drinow/MyNixieClock/MyNixie/Version2.0/Software/User/other.c

#include "other.h"

//显示数据，用1Byte表示1bit
uint8_t Nixie_HC595_Data[4][10]={0};

void Nixie_Delay(void)
{
  u32 i=0,j=0;
  for(;j<3;j++)
    for(;i<0xfffff;i++);
}

//把要点亮的数字坐标传给对应的位。
//参数：数字的行列坐标，和是否应该点亮
void Nixie_HC595_Num2Bit(u8 row,u8 line,u8 value)
{
  u8 product=0;
  product=(row+1)*10+line;
  switch((row+1)*10)//先大致分为4类，可减少判断次数
  {
    case 10:
    {
      switch(product)
      {
        case 10:if(value) HC595_Data[4]|= (1ul<<7); else HC595_Data[4]&=~(1ul<<7);break;
        case 11:if(value) HC595_Data[4]|= (1ul<<6); else HC595_Data[4]&=~(1ul<<6);break;
        case 12:if(value) HC595_Data[4]|= (1ul<<5); else HC595_Data[4]&=~(1ul<<5);break;
        case 13:if(value) HC595_Data[4]|= (1ul<<4); else HC595_Data[4]&=~(1ul<<4);break;
        case 14:if(value) HC595_Data[4]|= (1ul<<3); else HC595_Data[4]&=~(1ul<<3);break;
        case 15:if(value) HC595_Data[4]|= (1ul<<2); else HC595_Data[4]&=~(1ul<<2);break;
        case 16:if(value) HC595_Data[4]|= (1ul<<1); else HC595_Data[4]&=~(1ul<<1);break;
        case 17:if(value) HC595_Data[4]|= (1ul<<0); else HC595_Data[4]&=~(1ul<<0);break;
        case 18:if(value) HC595_Data[3]|= (1ul<<7); else HC595_Data[3]&=~(1ul<<7);break;
        case 19:if(value) HC595_Data[3]|= (1ul<<6); else HC595_Data[3]&=~(1ul<<6);break;
      }
    }
    break;
    case 20:
    {
      switch(product)
      {
        case 20:if(value) HC595_Data[3]|= (1ul<<5); else HC595_Data[3]&=~(1ul<<5);break;
        case 21:if(value) HC595_Data[3]|= (1ul<<4); else HC595_Data[3]&=~(1ul<<4);break;
        case 22:if(value) HC595_Data[3]|= (1ul<<3); else HC595_Data[3]&=~(1ul<<3);break;
        case 23:if(value) HC595_Data[3]|= (1ul<<2); else HC595_Data[3]&=~(1ul<<2);break;
        case 24:if(value) HC595_Data[3]|= (1ul<<1); else HC595_Data[3]&=~(1ul<<1);break;
        case 25:if(value) HC595_Data[3]|= (1ul<<0); else HC595_Data[3]&=~(1ul<<0);break;
        case 26:if(value) HC595_Data[2]|= (1ul<<7); else HC595_Data[2]&=~(1ul<<7);break;
        case 27:if(value) HC595_Data[2]|= (1ul<<6); else HC595_Data[2]&=~(1ul<<6);break;
        case 28:if(value) HC595_Data[2]|= (1ul<<5); else HC595_Data[2]&=~(1ul<<5);break;
        case 29:if(value) HC595_Data[2]|= (1ul<<4); else HC595_Data[2]&=~(1ul<<4);break;
      }
    }
    break;
    case 30:
    {
      switch(product)
      {
        case 30:if(value) HC595_Data[2]|= (1ul<<3); else HC595_Data[2]&=~(1ul<<3);break;
        case 31:if(value) HC595_Data[2]|= (1ul<<2); else HC595_Data[2]&=~(1ul<<2);break;
        case 32:if(value) HC595_Data[2]|= (1ul<<1); else HC595_Data[2]&=~(1ul<<1);break;
        case 33:if(value) HC595_Data[2]|= (1ul<<0); else HC595_Data[2]&=~(1ul<<0);break;
        case 34:if(value) HC595_Data[1]|= (1ul<<7); else HC595_Data[1]&=~(1ul<<7);break;
        case 35:if(value) HC595_Data[1]|= (1ul<<6); else HC595_Data[1]&=~(1ul<<6);break;
        case 36:if(value) HC595_Data[1]|= (1ul<<5); else HC595_Data[1]&=~(1ul<<5);break;
        case 37:if(value) HC595_Data[1]|= (1ul<<4); else HC595_Data[1]&=~(1ul<<4);break;
        case 38:if(value) HC595_Data[1]|= (1ul<<3); else HC595_Data[1]&=~(1ul<<3);break;
        case 39:if(value) HC595_Data[1]|= (1ul<<2); else HC595_Data[1]&=~(1ul<<2);break;
      }
    }
    break;
    case 40:
    {
      switch(product)
      {
        case 40:if(value) HC595_Data[1]|= (1ul<<1); else HC595_Data[1]&=~(1ul<<1);break;
        case 41:if(value) HC595_Data[1]|= (1ul<<0); else HC595_Data[1]&=~(1ul<<0);break;
        case 42:if(value) HC595_Data[0]|= (1ul<<7); else HC595_Data[0]&=~(1ul<<7);break;
        case 43:if(value) HC595_Data[0]|= (1ul<<6); else HC595_Data[0]&=~(1ul<<6);break;
        case 44:if(value) HC595_Data[0]|= (1ul<<5); else HC595_Data[0]&=~(1ul<<5);break;
        case 45:if(value) HC595_Data[0]|= (1ul<<4); else HC595_Data[0]&=~(1ul<<4);break;
        case 46:if(value) HC595_Data[0]|= (1ul<<3); else HC595_Data[0]&=~(1ul<<3);break;
        case 47:if(value) HC595_Data[0]|= (1ul<<2); else HC595_Data[0]&=~(1ul<<2);break;
        case 48:if(value) HC595_Data[0]|= (1ul<<1); else HC595_Data[0]&=~(1ul<<1);break;
        case 49:if(value) HC595_Data[0]|= (1ul<<0); else HC595_Data[0]&=~(1ul<<0);break;
      }
    }
    break;
    default:break;
  }
}

//将显示数据装载到595的输入缓存数组中
void Nixie_Load(u8 array[][10])
{
  u8 row,line;
  for(row=0;row<4;row++)
    for(line=0;line<10;line++)
  {
    Nixie_HC595_Num2Bit(row,line,array[row][line]);
  }
}

//将595的输入缓存数组的数据输出到595上
void Nixie_Update(void)
{
  hc595_WriteBytes(HC595_Data,sizeof(HC595_Data));
}

//自检程序。
void Nixie_Test(void)
{
    u8 state=0;
    u8 row;

    __disable_irq();
    memset((u8*)WS2812_RGB,0,sizeof(WS2812_RGB));
    WS2812_Send_Px();
    __enable_irq();

    Nixie_Light_Ctl(100);
    for(;state<10;state++)
    {
        //循环点亮
        memset(Nixie_HC595_Data,0,sizeof(Nixie_HC595_Data));
        for(row=0;row<4;row++)
        {
          Nixie_HC595_Data[row][state]=1;
        }

        Nixie_Load(Nixie_HC595_Data);
        Nixie_Update();

        Nixie_Delay();
    }
}


//将时间数据转换到HC595数组中。
extern __IO u16 LightLevel;
extern __IO u8 ForceLightOn;
void Nixie_TimeToHC595(void)
{
  memset(Nixie_HC595_Data,0,sizeof(Nixie_HC595_Data));
  Nixie_HC595_Data[0][GetTime.hour>>4]=1;
  Nixie_HC595_Data[1][GetTime.hour&0x0F]=1;
  Nixie_HC595_Data[2][GetTime.min>>4]=1;
  Nixie_HC595_Data[3][GetTime.min&0x0F]=1;
  
  Nixie_Load(Nixie_HC595_Data);
  Nixie_Update();
  
  if(LightLevel||ForceLightOn)
    Dot_Toggle();
  else
  {
    Dot1_OFF;Dot2_OFF;
  }
}

//将日期数据转换到HC595数组中。
void Nixie_DateToHC595(void)
{
  memset(Nixie_HC595_Data,0,sizeof(Nixie_HC595_Data));
  Nixie_HC595_Data[0][GetTime.month>>4]=1;
  Nixie_HC595_Data[1][GetTime.month&0x0F]=1;
  Nixie_HC595_Data[2][GetTime.date>>4]=1;
  Nixie_HC595_Data[3][GetTime.date&0x0F]=1;
  
	Dot1_OFF;Dot2_ON;
  Nixie_Load(Nixie_HC595_Data);
  Nixie_Update();
}

//将星期数据转换到HC595数组中。
void Nixie_WeekToHC595(void)
{
  memset(Nixie_HC595_Data,0,sizeof(Nixie_HC595_Data));

  Nixie_HC595_Data[2][GetTime.week>>4]=1;
  Nixie_HC595_Data[3][GetTime.week&0x0F]=1;
  
	Dot1_ON;Dot2_OFF;
  Nixie_Load(Nixie_HC595_Data);
  Nixie_Update();
}

//将温度数据转换到HC595数组中。
void Nixie_TempToHC595(void)
{
    memset(Nixie_HC595_Data,0,sizeof(Nixie_HC595_Data));

    Nixie_HC595_Data[0][(u8)(SHT20.HUMI_POLL)/10]=1;
    Nixie_HC595_Data[1][(u8)(SHT20.HUMI_POLL)%10]=1;
    Nixie_HC595_Data[2][(u8)((DS18B20_Temp+SHT20.TEMP_POLL)/2)/10]=1;
    Nixie_HC595_Data[3][(u8)((DS18B20_Temp+SHT20.TEMP_POLL)/2)%10]=1;

    Dot1_ON;Dot2_ON;
    Nixie_Load(Nixie_HC595_Data);
    Nixie_Update();
}


extern u8 SetChannel;
extern u8 NewNum;
u8 ChannelFlash=0;
extern u8  __IO Period_1S;
void Set_TimeToHC595(void)
{
	static u8 toggle=0;
  //按键按下
  if(NewNum!=0xff)
  {
    switch(SetChannel)
    {
      case CHANNEL0:if(NewNum>2)NewNum=0; SetTime.hour=(SetTime.hour&0x0f)|(NewNum<<4);NewNum=0xff; break;
      case CHANNEL1:if(SetTime.hour>=0x20&&NewNum>4)NewNum=4;SetTime.hour=(SetTime.hour&0xf0)|NewNum;NewNum=0xff;break;
      case CHANNEL2:if(NewNum>6)NewNum=0;SetTime.min=(SetTime.min&0x0f)|(NewNum<<4);NewNum=0xff;break;
      case CHANNEL3:SetTime.min=(SetTime.min&0xf0)|NewNum;NewNum=0xff;break;
      default :break;
    }
    SetChannel++;if(SetChannel>=4)SetChannel=0;
  }
  
  memset(Nixie_HC595_Data,0,sizeof(Nixie_HC595_Data));
  Nixie_HC595_Data[0][SetTime.hour>>4]=1;
  Nixie_HC595_Data[1][SetTime.hour&0x0F]=1;
  Nixie_HC595_Data[2][SetTime.min>>4]=1;
  Nixie_HC595_Data[3][SetTime.min&0x0F]=1;

  //被选中的通道闪烁
  if(ChannelFlash)
  {
    switch(SetChannel)
    {
      case CHANNEL0:Nixie_HC595_Data[0][SetTime.hour>>4]=0;break;
      case CHANNEL1:Nixie_HC595_Data[1][SetTime.hour&0x0F]=0;break;
      case CHANNEL2:Nixie_HC595_Data[2][SetTime.min>>4]=0;break;
      case CHANNEL3:Nixie_HC595_Data[3][SetTime.min&0x0F]=0;break;
      default :break;
    }
  }
    
  Nixie_Load(Nixie_HC595_Data);
  Nixie_Update();
  
	if(toggle)
	{
		toggle=~toggle;
		Dot1_ON;Dot2_ON;
	}
	else
	{
		toggle=~toggle;
		Dot1_OFF;Dot2_OFF;
	}
}

void Set_DateToHC595(void)
{
  if(NewNum!=0xff)
  {
    switch(SetChannel)
    {
      case CHANNEL0:if(NewNum>2)NewNum=0;SetTime.month=(SetTime.month&0x0f)|(NewNum<<4);NewNum=0xff;break;
      case CHANNEL1:SetTime.month=(SetTime.month&0xf0)|NewNum;NewNum=0xff;break;
      case CHANNEL2:if(NewNum>3)NewNum=0;SetTime.date=(SetTime.date&0x0f)|(NewNum<<4);NewNum=0xff;break;
      case CHANNEL3:if(SetTime.date>=0x30&&NewNum>1)NewNum=0;SetTime.date=(SetTime.date&0xf0)|NewNum;NewNum=0xff;break;
      default :break;
    }
    SetChannel++;if(SetChannel>=4)SetChannel=0;
  }
  
  memset(Nixie_HC595_Data,0,sizeof(Nixie_HC595_Data));
  Nixie_HC595_Data[0][SetTime.month>>4]=1;
  Nixie_HC595_Data[1][SetTime.month&0x0F]=1;
  Nixie_HC595_Data[2][SetTime.date>>4]=1;
  Nixie_HC595_Data[3][SetTime.date&0x0F]=1;

  //被选中的通道闪烁
  if(ChannelFlash)
  {
    switch(SetChannel)
    {
      case CHANNEL0:Nixie_HC595_Data[0][SetTime.month>>4]=0;break;
      case CHANNEL1:Nixie_HC595_Data[1][SetTime.month&0x0F]=0;break;
      case CHANNEL2:Nixie_HC595_Data[2][SetTime.date>>4]=0;break;
      case CHANNEL3:Nixie_HC595_Data[3][SetTime.date&0x0F]=0;break;
      default :break;
    }
  }
    
  Nixie_Load(Nixie_HC595_Data);
  Nixie_Update();
  
  Dot1_ON;Dot2_ON;
}

void Set_WeekToHC595(void)
{
  if(SetChannel<3)SetChannel=3;
  
  if(NewNum!=0xff)
  {
    switch(SetChannel)
    {
      case CHANNEL3:if(NewNum>7)NewNum=1;if(NewNum<1)NewNum=1;SetTime.week=(SetTime.week&0xf0)|NewNum;NewNum=0xff;break;
      default :break;
    }
    SetChannel++;if(SetChannel>=4)SetChannel=0;
  }
  
  memset(Nixie_HC595_Data,0,sizeof(Nixie_HC595_Data));
  Nixie_HC595_Data[3][SetTime.week&0x0F]=1;
  
  //被选中的通道闪烁
  if(ChannelFlash)
  {
    switch(SetChannel)
    {
      case CHANNEL3:Nixie_HC595_Data[3][SetTime.week&0x0F]=0;break;
      default :break;
    }
  }
    
  Nixie_Load(Nixie_HC595_Data);
  Nixie_Update();
  
  Dot1_OFF;Dot2_OFF;
}

void Set_YearToHC595(void)
{
  if(SetChannel<2)SetChannel=2;
  
  if(NewNum!=0xff)
  {
    switch(SetChannel)
    {
      case CHANNEL2:SetTime.year=(SetTime.year&0x0f)|(NewNum<<4);NewNum=0xff;break;
      case CHANNEL3:SetTime.year=(SetTime.year&0xf0)|NewNum;NewNum=0xff;break;
      default :break;
    }
    SetChannel++;if(SetChannel>=4)SetChannel=0;
  }
  
  memset(Nixie_HC595_Data,0,sizeof(Nixie_HC595_Data));
  Nixie_HC595_Data[0][2]=1;
  Nixie_HC595_Data[1][0]=1;
  Nixie_HC595_Data[2][SetTime.year>>4]=1;
  Nixie_HC595_Data[3][SetTime.year&0x0F]=1;

  //被选中的通道闪烁
  if(ChannelFlash)
  {
    switch(SetChannel)
    {
      case CHANNEL2:Nixie_HC595_Data[2][SetTime.year>>4]=0;break;
      case CHANNEL3:Nixie_HC595_Data[3][SetTime.year&0x0F]=0;break;
      default :break;
    }
  }
    
  Nixie_Load(Nixie_HC595_Data);
  Nixie_Update();
  
  Dot1_OFF;Dot2_OFF;
}

void Set_AlarmToHC595(void)
{
  //按键按下
  if(NewNum!=0xff)
  {
    switch(SetChannel)
    {
      case CHANNEL0:Alarm.hour=(Alarm.hour&0x0f)|(NewNum<<4);	NewNum=0xff; break;
      case CHANNEL1:Alarm.hour=(Alarm.hour&0xf0)|NewNum;			NewNum=0xff;break;
      case CHANNEL2:Alarm.min=(Alarm.min&0x0f)|(NewNum<<4);		NewNum=0xff;break;
      case CHANNEL3:Alarm.min=(Alarm.min&0xf0)|NewNum;				NewNum=0xff;break;
      default :break;
    }
    SetChannel++;if(SetChannel>=4)SetChannel=0;
  }
  
  memset(Nixie_HC595_Data,0,sizeof(Nixie_HC595_Data));
  Nixie_HC595_Data[0][Alarm.hour>>4]=1;
  Nixie_HC595_Data[1][Alarm.hour&0x0F]=1;
  Nixie_HC595_Data[2][Alarm.min>>4]=1;
  Nixie_HC595_Data[3][Alarm.min&0x0F]=1;

  //被选中的通道闪烁
  if(ChannelFlash)
  {
    switch(SetChannel)
    {
      case CHANNEL0:Nixie_HC595_Data[0][Alarm.hour>>4]=0;break;
      case CHANNEL1:Nixie_HC595_Data[1][Alarm.hour&0x0F]=0;break;
      case CHANNEL2:Nixie_HC595_Data[2][Alarm.min>>4]=0;break;
      case CHANNEL3:Nixie_HC595_Data[3][Alarm.min&0x0F]=0;break;
      default :break;
    }
    Dot1_ON;Dot2_OFF; 
  }
  else
  {
    Dot1_OFF;Dot2_ON; 
  }
    
  Nixie_Load(Nixie_HC595_Data);
  Nixie_Update();

}

extern u8 SetType;
void Nixie_Set_Show(void)
{
  switch(SetType)
  {
    case SETTIME:Set_TimeToHC595();break;
    case SETDATE:Set_DateToHC595();break;
    case SETWEEK:Set_WeekToHC595();break;
    case SETYEAR:Set_YearToHC595();break;
    case SETALARM:Set_AlarmToHC595();break;
    default:break;
  }
  ChannelFlash=~ChannelFlash;
}

//阴极保护程序，循环点亮其余未亮数字一小会
void Nixie_Cathode_Prevention(void)
{
  static u8 state=0;
  u32 i=0;
  uint8_t Nixie_Prevention_Data[4][10]={0};

  Nixie_Prevention_Data[0][state]=1;
  Nixie_Prevention_Data[1][state]=1;
  Nixie_Prevention_Data[2][state]=1;
  Nixie_Prevention_Data[3][state]=1;
  
  if((state++)==10)state=0;

  Nixie_Load(Nixie_Prevention_Data);
  Nixie_Update();
  
  for(i=0;i<0x5;i++);
  
  Nixie_Load(Nixie_HC595_Data);
  Nixie_Update();
}

void Nixie_Show(__IO u8 *state)
{
  static u8 cnt=0;
  switch(*state)
  {
    case DEFAULT:Nixie_TimeToHC595();break;
    case SHOWTEMP:Nixie_TempToHC595();cnt++;if(cnt>=4){cnt=0;Dot1_OFF;Dot2_OFF;*state=DEFAULT;Nixie_TimeToHC595();}break;
    case SHOWDATE:Nixie_DateToHC595();cnt++;if(cnt>=4){cnt=0;Dot1_OFF;Dot2_OFF;*state=DEFAULT;Nixie_TimeToHC595();}break;
    case SHOWWEEK:Nixie_WeekToHC595();cnt++;if(cnt>=4){cnt=0;Dot1_OFF;Dot2_OFF;*state=DEFAULT;Nixie_TimeToHC595();}break;
    default:break;
  }
}

extern __IO u16 LightLevel;
extern u8 Setting;
extern u8 SetChannel;
extern u8 SetType;
extern u8 NewNum;
extern u8 __IO ForceLightOn;
extern float Ruse,Guse,Buse;
float LightCoe=0;//亮度系数
void Nixie_DealRemote(__IO u8 *state)
{
  if(Setting==0)
  {
    switch(*state)
    {
        case DEFAULT:break;
        case SHOWSWITCH:  *state=DEFAULT;if(LightLevel==0)LightLevel=180;else {LightLevel=0;ForceLightOn=0;} 
                        Nixie_Light_Ctl(LightLevel);printf("LightLevel:%d\r\n",LightLevel);
                        EE_SaveConfig();
                        break;
        case LIGHT_UP:*state=DEFAULT;
                    LightLevel=LightLevel+20;if(LightLevel>=220)LightLevel=220;printf("LightLevel:%d\r\n",LightLevel);Nixie_Light_Ctl(LightLevel);
//                    LightCoe=LightCoe+0.15;if(LightCoe>=1)LightCoe=1;printf("LightCoe:%.1f\r\n",LightCoe);
                    EE_SaveConfig();
                    break;
        case LIGHT_DN:*state=DEFAULT;
                    LightLevel=LightLevel-20;if(LightLevel<=60)LightLevel=60;printf("LightLevel:%d\r\n",LightLevel);Nixie_Light_Ctl(LightLevel);
//                    LightCoe=LightCoe-0.15;if(LightCoe<=0.1)LightCoe=0.1;printf("LightCoe:%.1f\r\n",LightCoe);
                    EE_SaveConfig();
                    break;
        case PREV:  *state=DEFAULT;
                    LightCoe=LightCoe-0.15;if(LightCoe<=0.1)LightCoe=0.1;printf("LightCoe:%.1f\r\n",LightCoe);
                    EE_SaveConfig();
                    break;
        case NEXT:  *state=DEFAULT;
                    LightCoe=LightCoe+0.15;if(LightCoe>=1)LightCoe=1;printf("LightCoe:%.1f\r\n",LightCoe);
                    EE_SaveConfig();
                    break;
        case RGBSTATE:
                    *state=DEFAULT;
                    RGB_Msg.state++; 
                    if(RGB_Msg.state>=3)RGB_Msg.state=EFFECTS_ON;
//                    if(RGB_Msg.state==EFFECTS_OFF)
//                        {RGB_Msg.R=(u8)Ruse;RGB_Msg.G=(u8)Guse;RGB_Msg.B=(u8)Buse;}
                    if(RGB_Msg.state==EFFECTS_ON)//更新颜色信息
                        EE_SaveConfig();
                    break;
        case REDCOLOR:
                    *state=DEFAULT;
                    RGB_Msg.R=255,RGB_Msg.G=  0,RGB_Msg.B=  0;
                    WS2812_RGB[TUBE0][RED]=WS2812_RGB[TUBE0][GREEN]=WS2812_RGB[TUBE0][BLUE]=0;
                    WS2812_RGB[TUBE1][RED]=WS2812_RGB[TUBE1][GREEN]=WS2812_RGB[TUBE1][BLUE]=0;
                    WS2812_RGB[TUBE2][RED]=WS2812_RGB[TUBE2][GREEN]=WS2812_RGB[TUBE2][BLUE]=0;
                    WS2812_RGB[TUBE3][RED]=WS2812_RGB[TUBE3][GREEN]=WS2812_RGB[TUBE3][BLUE]=0;
                    RcdMAX_RGB[TUBE0][RED]=255;RcdMAX_RGB[TUBE0][GREEN]=0;RcdMAX_RGB[TUBE0][BLUE]=0;
                    RcdMAX_RGB[TUBE1][RED]=255;RcdMAX_RGB[TUBE1][GREEN]=0;RcdMAX_RGB[TUBE1][BLUE]=0;
                    RcdMAX_RGB[TUBE2][RED]=255;RcdMAX_RGB[TUBE2][GREEN]=0;RcdMAX_RGB[TUBE2][BLUE]=0;
                    RcdMAX_RGB[TUBE3][RED]=255;RcdMAX_RGB[TUBE3][GREEN]=0;RcdMAX_RGB[TUBE3][BLUE]=0;
                    RGB_Msg.mode=SINGLECOLOR;
                    if(RGB_Msg.state==EFFECTS_OFF)RGB_Msg.state=EFFECTS_ON;
                    EE_SaveConfig();
                    break;
        case ORGCOLOR:
                    *state=DEFAULT;
                    RGB_Msg.R=255,RGB_Msg.G=156,RGB_Msg.B=  0;
                    WS2812_RGB[TUBE0][RED]=WS2812_RGB[TUBE0][GREEN]=WS2812_RGB[TUBE0][BLUE]=0;
                    WS2812_RGB[TUBE1][RED]=WS2812_RGB[TUBE1][GREEN]=WS2812_RGB[TUBE1][BLUE]=0;
                    WS2812_RGB[TUBE2][RED]=WS2812_RGB[TUBE2][GREEN]=WS2812_RGB[TUBE2][BLUE]=0;
                    WS2812_RGB[TUBE3][RED]=WS2812_RGB[TUBE3][GREEN]=WS2812_RGB[TUBE3][BLUE]=0;
                    RcdMAX_RGB[TUBE0][RED]=255;RcdMAX_RGB[TUBE0][GREEN]=127;RcdMAX_RGB[TUBE0][BLUE]=0;
                    RcdMAX_RGB[TUBE1][RED]=255;RcdMAX_RGB[TUBE1][GREEN]=127;RcdMAX_RGB[TUBE1][BLUE]=0;
                    RcdMAX_RGB[TUBE2][RED]=255;RcdMAX_RGB[TUBE2][GREEN]=127;RcdMAX_RGB[TUBE2][BLUE]=0;
                    RcdMAX_RGB[TUBE3][RED]=255;RcdMAX_RGB[TUBE3][GREEN]=127;RcdMAX_RGB[TUBE3][BLUE]=0;
                    RGB_Msg.mode=SINGLECOLOR;
                    if(RGB_Msg.state==EFFECTS_OFF)RGB_Msg.state=EFFECTS_ON;
                    EE_SaveConfig();
                    break;
        case YELCOLOR:
                    *state=DEFAULT;
                    RGB_Msg.R=255,RGB_Msg.G=255,RGB_Msg.B=  0;
                    WS2812_RGB[TUBE0][RED]=WS2812_RGB[TUBE0][GREEN]=WS2812_RGB[TUBE0][BLUE]=0;
                    WS2812_RGB[TUBE1][RED]=WS2812_RGB[TUBE1][GREEN]=WS2812_RGB[TUBE1][BLUE]=0;
                    WS2812_RGB[TUBE2][RED]=WS2812_RGB[TUBE2][GREEN]=WS2812_RGB[TUBE2][BLUE]=0;
                    WS2812_RGB[TUBE3][RED]=WS2812_RGB[TUBE3][GREEN]=WS2812_RGB[TUBE3][BLUE]=0;
                    RcdMAX_RGB[TUBE0][RED]=255;RcdMAX_RGB[TUBE0][GREEN]=255;RcdMAX_RGB[TUBE0][BLUE]=0;
                    RcdMAX_RGB[TUBE1][RED]=255;RcdMAX_RGB[TUBE1][GREEN]=255;RcdMAX_RGB[TUBE1][BLUE]=0;
                    RcdMAX_RGB[TUBE2][RED]=255;RcdMAX_RGB[TUBE2][GREEN]=255;RcdMAX_RGB[TUBE2][BLUE]=0;
                    RcdMAX_RGB[TUBE3][RED]=255;RcdMAX_RGB[TUBE3][GREEN]=255;RcdMAX_RGB[TUBE3][BLUE]=0;
                    RGB_Msg.mode=SINGLECOLOR;
                    if(RGB_Msg.state==EFFECTS_OFF)RGB_Msg.state=EFFECTS_ON;
                    EE_SaveConfig();
                    break;
        case GRNCOLOR:
                    *state=DEFAULT;
                    RGB_Msg.R=  0,RGB_Msg.G=255,RGB_Msg.B=  0;
                    WS2812_RGB[TUBE0][RED]=WS2812_RGB[TUBE0][GREEN]=WS2812_RGB[TUBE0][BLUE]=0;
                    WS2812_RGB[TUBE1][RED]=WS2812_RGB[TUBE1][GREEN]=WS2812_RGB[TUBE1][BLUE]=0;
                    WS2812_RGB[TUBE2][RED]=WS2812_RGB[TUBE2][GREEN]=WS2812_RGB[TUBE2][BLUE]=0;
                    WS2812_RGB[TUBE3][RED]=WS2812_RGB[TUBE3][GREEN]=WS2812_RGB[TUBE3][BLUE]=0;
                    RcdMAX_RGB[TUBE0][RED]=0;RcdMAX_RGB[TUBE0][GREEN]=255;RcdMAX_RGB[TUBE0][BLUE]=0;
                    RcdMAX_RGB[TUBE1][RED]=0;RcdMAX_RGB[TUBE1][GREEN]=255;RcdMAX_RGB[TUBE1][BLUE]=0;
                    RcdMAX_RGB[TUBE2][RED]=0;RcdMAX_RGB[TUBE2][GREEN]=255;RcdMAX_RGB[TUBE2][BLUE]=0;
                    RcdMAX_RGB[TUBE3][RED]=0;RcdMAX_RGB[TUBE3][GREEN]=255;RcdMAX_RGB[TUBE3][BLUE]=0;
                    RGB_Msg.mode=SINGLECOLOR;
                    if(RGB_Msg.state==EFFECTS_OFF)RGB_Msg.state=EFFECTS_ON;
                    EE_SaveConfig();
                    break;
        case CYACOLOR:
                    *state=DEFAULT;
                    RGB_Msg.R=  0,RGB_Msg.G=255,RGB_Msg.B=255;
                    WS2812_RGB[TUBE0][RED]=WS2812_RGB[TUBE0][GREEN]=WS2812_RGB[TUBE0][BLUE]=0;
                    WS2812_RGB[TUBE1][RED]=WS2812_RGB[TUBE1][GREEN]=WS2812_RGB[TUBE1][BLUE]=0;
                    WS2812_RGB[TUBE2][RED]=WS2812_RGB[TUBE2][GREEN]=WS2812_RGB[TUBE2][BLUE]=0;
                    WS2812_RGB[TUBE3][RED]=WS2812_RGB[TUBE3][GREEN]=WS2812_RGB[TUBE3][BLUE]=0;
                    RcdMAX_RGB[TUBE0][RED]=0;RcdMAX_RGB[TUBE0][GREEN]=255;RcdMAX_RGB[TUBE0][BLUE]=255;
                    RcdMAX_RGB[TUBE1][RED]=0;RcdMAX_RGB[TUBE1][GREEN]=255;RcdMAX_RGB[TUBE1][BLUE]=255;
                    RcdMAX_RGB[TUBE2][RED]=0;RcdMAX_RGB[TUBE2][GREEN]=255;RcdMAX_RGB[TUBE2][BLUE]=255;
                    RcdMAX_RGB[TUBE3][RED]=0;RcdMAX_RGB[TUBE3][GREEN]=255;RcdMAX_RGB[TUBE3][BLUE]=255;
                    RGB_Msg.mode=SINGLECOLOR;
                    if(RGB_Msg.state==EFFECTS_OFF)RGB_Msg.state=EFFECTS_ON;
                    EE_SaveConfig();
                    break;
        case BLUCOLOR:
                    *state=DEFAULT;
                    RGB_Msg.R=  0,RGB_Msg.G=  0,RGB_Msg.B=255;
                    WS2812_RGB[TUBE0][RED]=WS2812_RGB[TUBE0][GREEN]=WS2812_RGB[TUBE0][BLUE]=0;
                    WS2812_RGB[TUBE1][RED]=WS2812_RGB[TUBE1][GREEN]=WS2812_RGB[TUBE1][BLUE]=0;
                    WS2812_RGB[TUBE2][RED]=WS2812_RGB[TUBE2][GREEN]=WS2812_RGB[TUBE2][BLUE]=0;
                    WS2812_RGB[TUBE3][RED]=WS2812_RGB[TUBE3][GREEN]=WS2812_RGB[TUBE3][BLUE]=0;
                    RcdMAX_RGB[TUBE0][RED]=0;RcdMAX_RGB[TUBE0][GREEN]=0;RcdMAX_RGB[TUBE0][BLUE]=255;
                    RcdMAX_RGB[TUBE1][RED]=0;RcdMAX_RGB[TUBE1][GREEN]=0;RcdMAX_RGB[TUBE1][BLUE]=255;
                    RcdMAX_RGB[TUBE2][RED]=0;RcdMAX_RGB[TUBE2][GREEN]=0;RcdMAX_RGB[TUBE2][BLUE]=255;
                    RcdMAX_RGB[TUBE3][RED]=0;RcdMAX_RGB[TUBE3][GREEN]=0;RcdMAX_RGB[TUBE3][BLUE]=255;
                    RGB_Msg.mode=SINGLECOLOR;
                    if(RGB_Msg.state==EFFECTS_OFF)RGB_Msg.state=EFFECTS_ON;
                    EE_SaveConfig();
                    break;
        case PURCOLOR:
                    *state=DEFAULT;
                    RGB_Msg.R=255,RGB_Msg.G=  0,RGB_Msg.B=255;
                    WS2812_RGB[TUBE0][RED]=WS2812_RGB[TUBE0][GREEN]=WS2812_RGB[TUBE0][BLUE]=0;
                    WS2812_RGB[TUBE1][RED]=WS2812_RGB[TUBE1][GREEN]=WS2812_RGB[TUBE1][BLUE]=0;
                    WS2812_RGB[TUBE2][RED]=WS2812_RGB[TUBE2][GREEN]=WS2812_RGB[TUBE2][BLUE]=0;
                    WS2812_RGB[TUBE3][RED]=WS2812_RGB[TUBE3][GREEN]=WS2812_RGB[TUBE3][BLUE]=0;
                    RcdMAX_RGB[TUBE0][RED]=255;RcdMAX_RGB[TUBE0][GREEN]=0;RcdMAX_RGB[TUBE0][BLUE]=255;
                    RcdMAX_RGB[TUBE1][RED]=255;RcdMAX_RGB[TUBE1][GREEN]=0;RcdMAX_RGB[TUBE1][BLUE]=255;
                    RcdMAX_RGB[TUBE2][RED]=255;RcdMAX_RGB[TUBE2][GREEN]=0;RcdMAX_RGB[TUBE2][BLUE]=255;
                    RcdMAX_RGB[TUBE3][RED]=255;RcdMAX_RGB[TUBE3][GREEN]=0;RcdMAX_RGB[TUBE3][BLUE]=255;
                    RGB_Msg.mode=SINGLECOLOR;
                    if(RGB_Msg.state==EFFECTS_OFF)RGB_Msg.state=EFFECTS_ON;
                    EE_SaveConfig();
                    break;
        case WHTCOLOR:
                    *state=DEFAULT;
                    RGB_Msg.R=255,RGB_Msg.G=255,RGB_Msg.B=255;
                    WS2812_RGB[TUBE0][RED]=WS2812_RGB[TUBE0][GREEN]=WS2812_RGB[TUBE0][BLUE]=0;
                    WS2812_RGB[TUBE1][RED]=WS2812_RGB[TUBE1][GREEN]=WS2812_RGB[TUBE1][BLUE]=0;
                    WS2812_RGB[TUBE2][RED]=WS2812_RGB[TUBE2][GREEN]=WS2812_RGB[TUBE2][BLUE]=0;
                    WS2812_RGB[TUBE3][RED]=WS2812_RGB[TUBE3][GREEN]=WS2812_RGB[TUBE3][BLUE]=0;
                    RcdMAX_RGB[TUBE0][RED]=RcdMAX_RGB[TUBE0][GREEN]=RcdMAX_RGB[TUBE0][BLUE]=255;
                    RcdMAX_RGB[TUBE1][RED]=RcdMAX_RGB[TUBE1][GREEN]=RcdMAX_RGB[TUBE1][BLUE]=255;
                    RcdMAX_RGB[TUBE2][RED]=RcdMAX_RGB[TUBE2][GREEN]=RcdMAX_RGB[TUBE2][BLUE]=255;
                    RcdMAX_RGB[TUBE3][RED]=RcdMAX_RGB[TUBE3][GREEN]=RcdMAX_RGB[TUBE3][BLUE]=255;
                    RGB_Msg.mode=SINGLECOLOR;
                    if(RGB_Msg.state==EFFECTS_OFF)RGB_Msg.state=EFFECTS_ON;//   RGBType=WHTCOLOR;
                    EE_SaveConfig();
                    break;
        case COLORFUL:
                    *state=DEFAULT;
                    RGB_Msg.R=255,RGB_Msg.G=255,RGB_Msg.B=255;
                    if(RGB_Msg.mode!=MULTICOLOR)
                    {
                        RGB_Msg.mode=MULTICOLOR;
                        WS2812_RGB[TUBE0][RED]=WS2812_RGB[TUBE0][GREEN]=WS2812_RGB[TUBE0][BLUE]=0;
                        WS2812_RGB[TUBE1][RED]=WS2812_RGB[TUBE1][GREEN]=WS2812_RGB[TUBE1][BLUE]=0;
                        WS2812_RGB[TUBE2][RED]=WS2812_RGB[TUBE2][GREEN]=WS2812_RGB[TUBE2][BLUE]=0;
                        WS2812_RGB[TUBE3][RED]=WS2812_RGB[TUBE3][GREEN]=WS2812_RGB[TUBE3][BLUE]=0;
                        RcdMAX_RGB[TUBE0][RED]=255;RcdMAX_RGB[TUBE0][GREEN]=255;RcdMAX_RGB[TUBE0][BLUE]=255;
                        RcdMAX_RGB[TUBE1][RED]=255;RcdMAX_RGB[TUBE1][GREEN]=255;RcdMAX_RGB[TUBE1][BLUE]=255;
                        RcdMAX_RGB[TUBE2][RED]=255;RcdMAX_RGB[TUBE2][GREEN]=255;RcdMAX_RGB[TUBE2][BLUE]=255;
                        RcdMAX_RGB[TUBE3][RED]=255;RcdMAX_RGB[TUBE3][GREEN]=255;RcdMAX_RGB[TUBE3][BLUE]=255;
                    }
                    else 
                    {
                        RGB_Msg.mode=RAINBOW;
                        RainBowstate[0]=0;
                        RainBowstate[1]=1;
                        RainBowstate[2]=2;
                        RainBowstate[3]=3;
                        WS2812_RGB[TUBE0][RED]=255;WS2812_RGB[TUBE0][GREEN]=0;WS2812_RGB[TUBE0][BLUE]=0;
                        WS2812_RGB[TUBE1][RED]=255;WS2812_RGB[TUBE1][GREEN]=0;WS2812_RGB[TUBE1][BLUE]=255;
                        WS2812_RGB[TUBE2][RED]=0;WS2812_RGB[TUBE2][GREEN]=0;WS2812_RGB[TUBE2][BLUE]=255;
                        WS2812_RGB[TUBE3][RED]=0;WS2812_RGB[TUBE3][GREEN]=255;WS2812_RGB[TUBE3][BLUE]=255;
                        RcdMAX_RGB[TUBE0][RED]=255;RcdMAX_RGB[TUBE0][GREEN]=255;RcdMAX_RGB[TUBE0][BLUE]=255;
                        RcdMAX_RGB[TUBE1][RED]=255;RcdMAX_RGB[TUBE1][GREEN]=255;RcdMAX_RGB[TUBE1][BLUE]=255;
                        RcdMAX_RGB[TUBE2][RED]=255;RcdMAX_RGB[TUBE2][GREEN]=255;RcdMAX_RGB[TUBE2][BLUE]=255;
                        RcdMAX_RGB[TUBE3][RED]=255;RcdMAX_RGB[TUBE3][GREEN]=255;RcdMAX_RGB[TUBE3][BLUE]=255;
                    }
                    if(RGB_Msg.state==EFFECTS_OFF)RGB_Msg.state=EFFECTS_ON;
                    EE_SaveConfig();
                    break;
        case SETTING:
                    *state=DEFAULT;Setting=1;
                    break;
        default:if(*state!=SHOWTEMP&&*state!=SHOWDATE&&*state!=SHOWWEEK)*state=DEFAULT;break;
    }
  }
  else
  {
    switch(*state)
    {
      case DEFAULT:break;//设置模式下，显示函数拿出来了
      case SHOWSWITCH:*state=DEFAULT;if(LightLevel==0)LightLevel=100;Nixie_Light_Ctl(LightLevel);break;			
      case SET_TYPE:*state=DEFAULT;SetType++;if(SetType>=5)SetType=0;printf("type:%d\r\n",SetType);break;
      case CHANNEL_DN:*state=DEFAULT;SetChannel--;if(SetChannel==0xff)SetChannel=3;break;
      case CHANNEL_UP:*state=DEFAULT;SetChannel++;if(SetChannel==4)SetChannel=0;break;
      case NUM0:*state=DEFAULT;NewNum=0;break;
      case NUM1:*state=DEFAULT;NewNum=1;break;
      case NUM2:*state=DEFAULT;NewNum=2;break;
      case NUM3:*state=DEFAULT;NewNum=3;break;
      case NUM4:*state=DEFAULT;NewNum=4;break;
      case NUM5:*state=DEFAULT;NewNum=5;break;
      case NUM6:*state=DEFAULT;NewNum=6;break;
      case NUM7:*state=DEFAULT;NewNum=7;break;
      case NUM8:*state=DEFAULT;NewNum=8;break;
      case NUM9:*state=DEFAULT;NewNum=9;break;
      case VALUE_UP:*state=DEFAULT;break;
      case VALUE_DN:*state=DEFAULT;break;
      case SETTING :*state=DEFAULT;
      printf("SET:\r\n Dt:20%02x-%02x-%2x Tm:%02x:%02x:%02x  Wk:%2x\r\n"\
						,SetTime.year,SetTime.month,SetTime.date,SetTime.hour,SetTime.min,SetTime.sec,SetTime.week);
      Setting=0;
      break;
      default:*state=DEFAULT;break;
    }  
  }
}

extern u16 LightTime1H;
extern u16 RunTime1H;
extern __IO u8 AlarmSwitch;
extern u8 FirstRunFlag;
void EE_SaveConfig(void)
{

    EE_WriteVariable(VirtAddVarTab[LightTimeAddr],LightTime1H);
    EE_WriteVariable(VirtAddVarTab[LightLevelAddr],LightLevel);
    EE_WriteVariable(VirtAddVarTab[RGBStateAddr],RGB_Msg.state);
    EE_WriteVariable(VirtAddVarTab[AlarmAddr],((u16)Alarm.hour<<8)|Alarm.min);
    EE_WriteVariable(VirtAddVarTab[RunTimeAddr],RunTime1H);
    EE_WriteVariable(VirtAddVarTab[RMsgAddr],RGB_Msg.R);
    EE_WriteVariable(VirtAddVarTab[GMsgAddr],RGB_Msg.G);
    EE_WriteVariable(VirtAddVarTab[BMsgAddr],RGB_Msg.B);
    EE_WriteVariable(VirtAddVarTab[RGBModeAddr],RGB_Msg.mode);
    EE_WriteVariable(VirtAddVarTab[AlarmSwitchAddr],AlarmSwitch);
    EE_WriteVariable(VirtAddVarTab[FirstRunFlagAddr],FirstRunFlag);
    EE_WriteVariable(VirtAddVarTab[LightCoeAddr],(u16)(LightCoe*100));
}

void HC595_PWM_Init(void)
{
  {
    GPIO_InitTypeDef GPIO_InitStructure;

    /* GPIOB clock enable */
    RCC_APB2PeriphClockCmd(RCC_APB2Periph_GPIOA, ENABLE); 

    /* 配置呼吸灯用到的PB0引脚 */
    GPIO_InitStructure.GPIO_Pin =  GPIO_Pin_3 ;
    GPIO_InitStructure.GPIO_Mode = GPIO_Mode_AF_PP;		    // 复用推挽输出
    GPIO_InitStructure.GPIO_Speed = GPIO_Speed_50MHz;
    GPIO_Init(GPIOA, &GPIO_InitStructure);
  }
  
  {
  	TIM_TimeBaseInitTypeDef  TIM_TimeBaseStructure;
    TIM_OCInitTypeDef  TIM_OCInitStructure;																				
    
    /* 设置TIM3CLK 时钟为72MHZ */
    RCC_APB1PeriphClockCmd(RCC_APB1Periph_TIM2, ENABLE); 					//使能TIM3时钟

    /* 基本定时器配置 */		 
    TIM_TimeBaseStructure.TIM_Period = 255;       							  //当定时器从0计数到255，即为266次，为一个定时周期
    TIM_TimeBaseStructure.TIM_Prescaler = 1999;	    							//设置预分频：
    TIM_TimeBaseStructure.TIM_ClockDivision = TIM_CKD_DIV1 ;			//设置时钟分频系数：不分频(这里用不到)
    TIM_TimeBaseStructure.TIM_CounterMode = TIM_CounterMode_Up;  	//向上计数模式
    TIM_TimeBaseInit(TIM2, &TIM_TimeBaseStructure);

    /* PWM模式配置 */
    TIM_OCInitStructure.TIM_OCMode = TIM_OCMode_PWM1;	    				//配置为PWM模式1
    TIM_OCInitStructure.TIM_OutputState = TIM_OutputState_Enable;	//使能输出
    TIM_OCInitStructure.TIM_Pulse = 100;										  			//设置初始PWM脉冲宽度为0	
    TIM_OCInitStructure.TIM_OCPolarity = TIM_OCPolarity_Low;  	  //当定时器计数值小于CCR1_Val时为低电平

    TIM_OC4Init(TIM2, &TIM_OCInitStructure);	 									//使能通道3
    

    TIM_OC4PreloadConfig(TIM2, TIM_OCPreload_Enable);						//使能预装载	

    TIM_ARRPreloadConfig(TIM2, ENABLE);			 										//使能TIM3重载寄存器ARR

    /* TIM3 enable counter */
    TIM_Cmd(TIM2, ENABLE);                   										//使能定时器3	
  }
}

static void Nixie_Light_delay(void)
{
	uint32_t i=0;
	for(i=0;i<13000;i++);
}
//PWM亮度控制
//0-255亮度等级
void Nixie_Light_Ctl(u8 value)
{
    u8 i=0;
    u8 lastValue=TIM2->CCR4;
    if(value>=lastValue) //亮度增加
    {
        for(i=lastValue;i<value;i++)
        {
            TIM2->CCR4=i;
            Nixie_Light_delay();
        }
    }
    else {
        for(i=lastValue;i>value;i--)
        {
            TIM2->CCR4=i;
            Nixie_Light_delay();
        }
        TIM2->CCR4=i;//确保i=0;
    }
}

void KEY_GPIO_Config(void)
{
    GPIO_InitTypeDef GPIO_InitStructure;

    RCC_APB2PeriphClockCmd( RCC_KEY1|RCC_KEY2|RCC_KEY3|RCC_KEY4, ENABLE); 

    //KEY1
    GPIO_InitStructure.GPIO_Pin = GPIO_PIN_KEY1;
    GPIO_InitStructure.GPIO_Mode = GPIO_Mode_IPU;   
    GPIO_InitStructure.GPIO_Speed = GPIO_Speed_50MHz; 
    GPIO_Init(GPIO_PORT_KEY1, &GPIO_InitStructure);

    //KEY2
    GPIO_InitStructure.GPIO_Pin = GPIO_PIN_KEY2;
    GPIO_InitStructure.GPIO_Mode = GPIO_Mode_IPU;   
    GPIO_InitStructure.GPIO_Speed = GPIO_Speed_50MHz; 
    GPIO_Init(GPIO_PORT_KEY2, &GPIO_InitStructure);
    
    //KEY3
    GPIO_InitStructure.GPIO_Pin = GPIO_PIN_KEY3;
    GPIO_InitStructure.GPIO_Mode = GPIO_Mode_IPU;   
    GPIO_InitStructure.GPIO_Speed = GPIO_Speed_50MHz; 
    GPIO_Init(GPIO_PORT_KEY3, &GPIO_InitStructure);
    
    //KEY4
    GPIO_InitStructure.GPIO_Pin = GPIO_PIN_KEY4;
    GPIO_InitStructure.GPIO_Mode = GPIO_Mode_IPU;   
    GPIO_InitStructure.GPIO_Speed = GPIO_Speed_50MHz; 
    GPIO_Init(GPIO_PORT_KEY4, &GPIO_InitStructure);
}


uint8_t Read_Key(uint8_t key_num)
{
    switch(key_num)
    {
        case KEY1:return GPIO_ReadInputDataBit(GPIO_PORT_KEY1, GPIO_PIN_KEY1);
        case KEY2:return GPIO_ReadInputDataBit(GPIO_PORT_KEY2, GPIO_PIN_KEY2);
        case KEY3:return GPIO_ReadInputDataBit(GPIO_PORT_KEY3, GPIO_PIN_KEY3);
        case KEY4:return GPIO_ReadInputDataBit(GPIO_PORT_KEY4, GPIO_PIN_KEY4);
        default: return 1;
    }
}

void MyTest(void)
{

}
