drinow/MyNixieClock/MyNixie/Version2.0/Software/User/remote.c

#include "remote.h"
//////////////////////////////////////////////////////////////////////////////////	 
//本程序只供学习使用，未经作者许可，不得用于其它任何用途
//Mini STM32开发板
//红外遥控接收 驱动代码		   
//正点原子@ALIENTEK
//技术论坛:www.openedv.com
//修改日期:2010/6/17 
//版本：V1.0
//版权所有，盗版必究。
//Copyright(C) 正点原子 2009-2019
//All rights reserved
////////////////////////////////////////////////////////////////////////////////// 	  

void Remote_Delay_10us(u8 cnt)
{
  for(;cnt>0;cnt--)
  {
  //10us
  __NOP();__NOP();__NOP();__NOP();__NOP();__NOP();__NOP();__NOP();__NOP();__NOP();__NOP();__NOP();
  __NOP();__NOP();__NOP();__NOP();__NOP();__NOP();__NOP();__NOP();__NOP();__NOP();__NOP();__NOP();
  __NOP();__NOP();__NOP();__NOP();__NOP();__NOP();__NOP();__NOP();__NOP();__NOP();__NOP();__NOP();
  __NOP();__NOP();__NOP();__NOP();__NOP();__NOP();__NOP();__NOP();__NOP();__NOP();__NOP();__NOP();
  __NOP();__NOP();__NOP();__NOP();__NOP();__NOP();__NOP();__NOP();__NOP();__NOP();__NOP();__NOP();
  __NOP();__NOP();__NOP();__NOP();__NOP();__NOP();__NOP();__NOP();__NOP();__NOP();__NOP();__NOP();
  __NOP();__NOP();__NOP();__NOP();__NOP();__NOP();__NOP();__NOP();__NOP();__NOP();__NOP();__NOP();
  __NOP();__NOP();__NOP();__NOP();__NOP();
  }
}

u32 Remote_Odr=0;  	 //命令暂存处
u8  Remote_Cnt=0;    //按键次数,此次按下键的次数
u8  Remote_Rdy=0;    //红外接收到数据    
//初始化红外接收引脚的设置
//开启中断,并映射 
void Remote_Init(void)
{							 
	GPIO_InitTypeDef GPIO_InitStructure;	//GPIO
//	NVIC_InitTypeDef NVIC_InitStructure;	//中断
	EXTI_InitTypeDef EXTI_InitStructure;	//外部中断线
 		 
	RCC_APB2PeriphClockCmd(	RCC_APB2Periph_GPIOB|RCC_APB2Periph_AFIO, ENABLE );	  
 
	GPIO_InitStructure.GPIO_Pin = GPIO_Pin_7;
	GPIO_InitStructure.GPIO_Mode = GPIO_Mode_IPU ;  //上拉输入
	GPIO_InitStructure.GPIO_Speed = GPIO_Speed_50MHz;
	GPIO_Init(GPIOB, &GPIO_InitStructure);  
 
	GPIO_EXTILineConfig(GPIO_PortSourceGPIOB, GPIO_PinSource7);  	//选择PA1所在的GPIO管脚用作外部中断线路EXIT1		
 
	EXTI_InitStructure.EXTI_Line = EXTI_Line7;	//外部线路EXIT1
	EXTI_InitStructure.EXTI_Mode = EXTI_Mode_Interrupt;			//设外外部中断模式:EXTI线路为中断请求  EXTI_Mode_Event ;//设置 EXTI线路为事件请求 
	EXTI_InitStructure.EXTI_Trigger = EXTI_Trigger_Falling;  //外部中断触发沿选择:设置输入线路下降沿为中断请求
	EXTI_InitStructure.EXTI_LineCmd = ENABLE;		//使能外部中断新状态
	EXTI_Init(&EXTI_InitStructure);		//根据EXTI_InitStruct中指定的参数初始化外设EXTI寄存器	
}   
//检测脉冲宽度
//最长脉宽为5ms
//返回值:x,代表脉宽为x*20us(x=1~250);
u8 Pulse_Width_Check(void)
{
    u8 t=0;	 
    while(RDATA)
    {	 
      t++;
      //例程精确定时为20us很准，但是对于粗略延时来说仿真为150us才好用
      Remote_Delay_10us(15);					 
      if(t==250)return t; //超时溢出
    }
    return t;
}			   
//处理红外接收  
/*-------------------------协议--------------------------
开始拉低9ms,接着是一个4.5ms的高脉冲,通知器件开始传送数据了
接着是发送4个8位二进制码,第一二个是遥控识别码(REMOTE_ID),第一个为
正码(0),第二个为反码(255),接着两个数据是键值,第一个为正码
第二个为反码.发送完后40ms,遥控再发送一个9ms低,2ms高的脉冲,
表示按键的次数,出现一次则证明只按下了一次,如果出现多次,则可
以认为是持续按下该键.
---------------------------------------------------------*/		 
//外部中断服务程序	   
void EXTI9_5_IRQHandler(void)
{       
	u8 res=0;
  u8 OK=0; 
  u8 RODATA=0;   		
  if(EXTI_GetITStatus(EXTI_Line7) != RESET)
  {  
    while(1)
      {        
          if(RDATA)//有高脉冲出现
          {
              res=Pulse_Width_Check();//获得此次高脉冲宽度       
              if(res==250)break;//非有用信号
              if(res>=200&&res<250)OK=1; //获得前导位(4.5ms)
              else if(res>=85&&res<200)  //按键次数加一(2ms)
              {  							    		 
                  Remote_Rdy=1;//接受到数据
                  Remote_Cnt++;//按键次数增加
                  break;
              }
              else if(res>=50&&res<85)RODATA=1;//1.5ms
              else if(res>=10&&res<50)RODATA=0;//500us
              if(OK)
              {
                  Remote_Odr<<=1;
                  Remote_Odr+=RODATA; 
                  Remote_Cnt=0; //按键次数清零
              }   
          }			 						 
      } 	 	    
    EXTI_ClearITPendingBit(EXTI_Line7);  //清除EXTI1线路挂起位   
  }    
}  
//处理红外键盘
//返回相应的键值
u8 Remote_Process(void)
{               
    u8 t1,t2;   
    t1=Remote_Odr>>24; //得到地址码
    t2=(Remote_Odr>>16)&0xff;//得到地址反码 
    if(Remote_Rdy)
    {
        Remote_Rdy=0;//清除标记 
        if(t1==(u8)~t2&&t1==REMOTE_ID)//检验遥控识别码(ID)及地址 
        { 
            t1=Remote_Odr>>8;
            t2=Remote_Odr; 	
            if(t1==(u8)~t2)return t1; //处理键值
        }
    }
    return 0;
}
