drinow/MyNixieClock/MyNixie/Version2.0/Software/User/include.h

#ifndef __INCLUDE_H
#define __INCLUDE_H

#include "stm32f10x.h"
#include "stdio.h"
#include <string.h>
#include "bsp_SysTick.h"
#include "bsp_led.h"
#include "bsp_usart1.h"
#include "ds3231.h"
#include "bsp_i2c_gpio.h"
#include "bsp_beep.h"
#include "bsp_ds18b20.h"
#include "WS2812B.h"
#include "other.h"
#include "remote.h"
#include "sys.h"
#include "bsp_74hc595.h"
#include "eeprom.h"
#include "SHT2x.h"

#endif
