drinow/MyNixieClock/MyNixie/Version2.0/Software/User/bsp_beep.h

#ifndef __BSP_BEEP_H
#define __BSP_BEEP_H

#include "include.h"

#define Beep(a)	if (a)	\
                  GPIO_SetBits(GPIOB,GPIO_Pin_6);\
                else		\
                  GPIO_ResetBits(GPIOB,GPIO_Pin_6)
          
								
void BeepInit(void);
void Beep_State(u32 num);
void Beep_Alarm(void);
void Beep_OnTimeAlarm(void);
								
#endif
