drinow/MyNixieClock/MyNixie/Version2.0/Software/User/bsp_usart1.c

/**
  ******************************************************************************
  * @file    bsp_usart1.c
  * @author  fire
  * @version V1.0
  * @date    2013-xx-xx
  * @brief   重现c库printf函数到usart端口
  ******************************************************************************
  * @attention
  *
  * 实验平台:野火 iSO-MINI STM32 开发板 
  * 论坛    :http://www.chuxue123.com
  * 淘宝    :http://firestm32.taobao.com
  *
  ******************************************************************************
  */ 
  
#include "bsp_usart1.h"

 /**
  * @brief  USART1 GPIO 配置,工作模式配置。115200 8-N-1
  * @param  无
  * @retval 无
  */
void USART1_Config(void)
{
		GPIO_InitTypeDef GPIO_InitStructure;
		USART_InitTypeDef USART_InitStructure;
		
		/* config USART1 clock */
		RCC_APB2PeriphClockCmd(RCC_APB2Periph_USART1 | RCC_APB2Periph_GPIOA, ENABLE);
		
		/* USART1 GPIO config */
		/* Configure USART1 Tx (PA.09) as alternate function push-pull */
		GPIO_InitStructure.GPIO_Pin = GPIO_Pin_9;
		GPIO_InitStructure.GPIO_Mode = GPIO_Mode_AF_PP;
		GPIO_InitStructure.GPIO_Speed = GPIO_Speed_50MHz;
		GPIO_Init(GPIOA, &GPIO_InitStructure);
	
		/* Configure USART1 Rx (PA.10) as input floating */
		GPIO_InitStructure.GPIO_Pin = GPIO_Pin_10;
		GPIO_InitStructure.GPIO_Mode = GPIO_Mode_IN_FLOATING;
		GPIO_Init(GPIOA, &GPIO_InitStructure);
			
		/* USART1 mode config */
		USART_InitStructure.USART_BaudRate = 115200;
		USART_InitStructure.USART_WordLength = USART_WordLength_8b;
		USART_InitStructure.USART_StopBits = USART_StopBits_1;
		USART_InitStructure.USART_Parity = USART_Parity_No ;
		USART_InitStructure.USART_HardwareFlowControl = USART_HardwareFlowControl_None;
		USART_InitStructure.USART_Mode = USART_Mode_Rx | USART_Mode_Tx;
		USART_Init(USART1, &USART_InitStructure); 
		USART_ITConfig(USART1, USART_IT_RXNE, ENABLE);
		USART_Cmd(USART1, ENABLE);
}


void USART1_IRQHandler(void)
{
  u8 data;
	if(USART_GetITStatus(USART1, USART_IT_RXNE) != RESET)
	{ 	
	  //ch = USART1->DR;
		data=USART_ReceiveData(USART1);
    printf("%c\r\n",data);
	} 
}

///重定向c库函数printf到USART1
int fputc(int ch, FILE *f)
{
		/* 发送一个字节数据到USART1 */
		USART_SendData(USART1, (uint8_t) ch);
		
		/* 等待发送完毕 */
		while (USART_GetFlagStatus(USART1, USART_FLAG_TC) == RESET);		
	
		return (ch);
}

///重定向c库函数scanf到USART1
int fgetc(FILE *f)
{
		/* 等待串口1输入数据 */
		while (USART_GetFlagStatus(USART1, USART_FLAG_RXNE) == RESET);

		return (int)USART_ReceiveData(USART1);
}

//发送一个字节
void UART_PutChar(USART_TypeDef* USARTx, uint8_t Data)  
{  
    USART_SendData(USARTx, Data);  
    while(USART_GetFlagStatus(USARTx, USART_FLAG_TC) == RESET){}  
} 

//发送一个数组
void USART_SendString(USART_TypeDef* USARTx, u8* pBuffer, u16 len)
{
   u16 i = 0; 
    
   for (i = 0; i < len; i++)
   {             
       USART_SendData(USARTx, pBuffer[i]);
       while (USART_GetFlagStatus(USARTx, USART_FLAG_TC) == RESET);                               
   }
}

/*********************************************END OF FILE**********************/
