drinow/MyNixieClock/MyNixie/Version2.0/Software/User/bsp_usart1.h

#ifndef __USART1_H
#define	__USART1_H
#include "include.h"

void USART1_Config(void);
void USART_SendString(USART_TypeDef* USARTx, u8* pBuffer, u16 len);
void UART_PutChar(USART_TypeDef* USARTx, uint8_t Data);
#endif /* __USART1_H */
